leonardoward/gps-development-boards/Images/IMG_20210819_091816.jpg

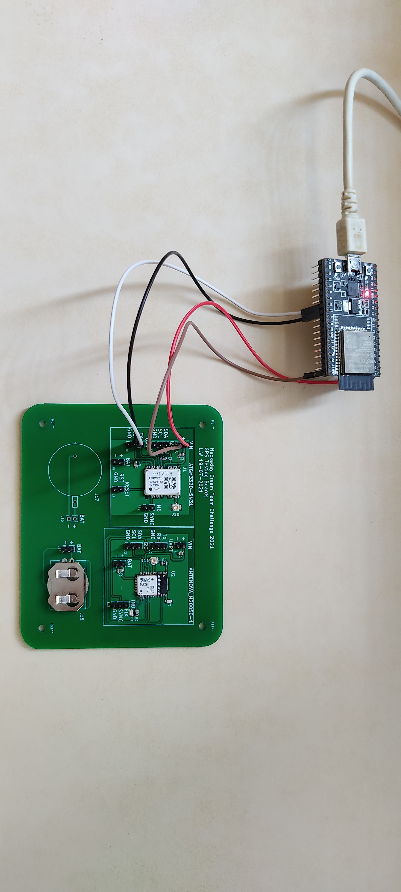
Images/IMG_20210819_091816.jpg
