leonardoward/gps-development-boards/Images/IMG_20210819_091819.jpg

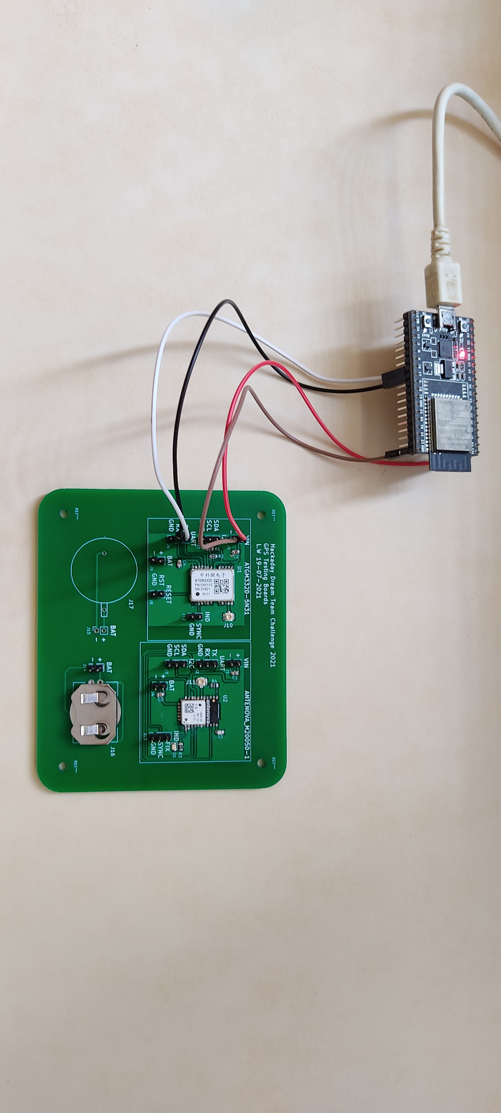
Images/IMG_20210819_091819.jpg
