leonardoward/gps-development-boards/Images/IMG_20210819_091824.jpg

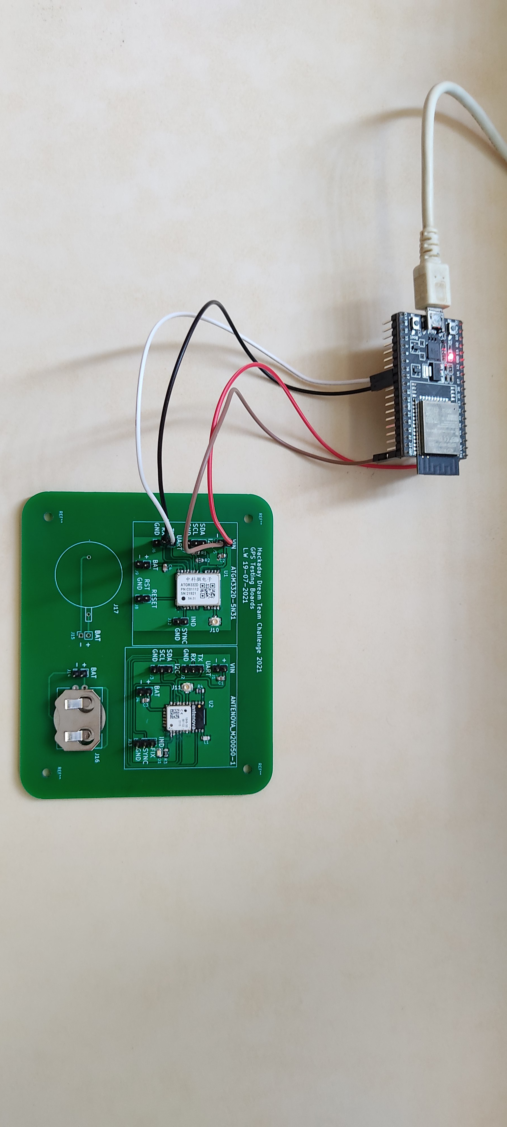
Images/IMG_20210819_091824.jpg
