leonardoward/gps-development-boards/Images/IMG_20210819_091829.jpg

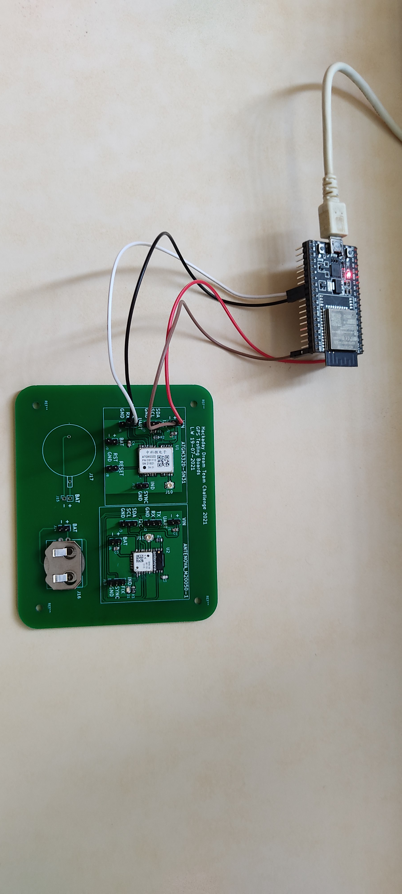
Images/IMG_20210819_091829.jpg
