leonardoward/gps-development-boards/Images/IMG_20210819_091835.jpg

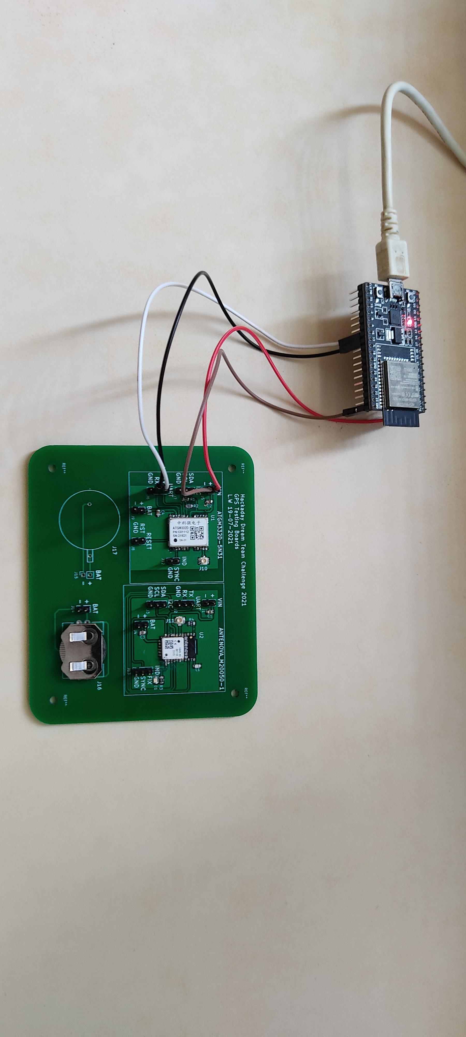
Images/IMG_20210819_091835.jpg
