leonardoward/gps-development-boards/Images/IMG_20210819_091837.jpg

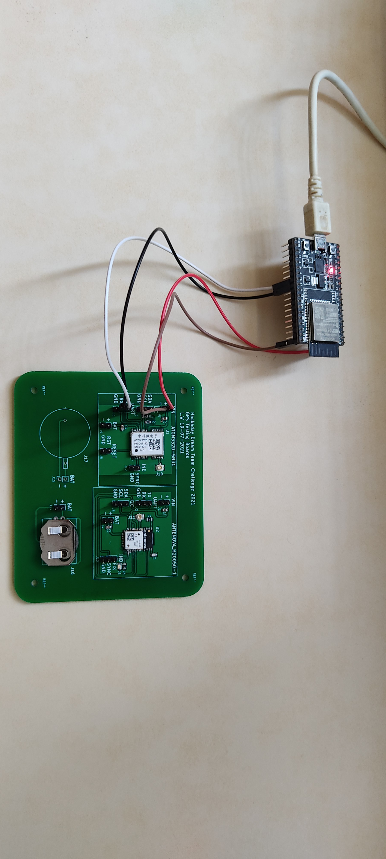
Images/IMG_20210819_091837.jpg
