leonardoward/gps-development-boards/Images/IMG_20210819_092154.jpg

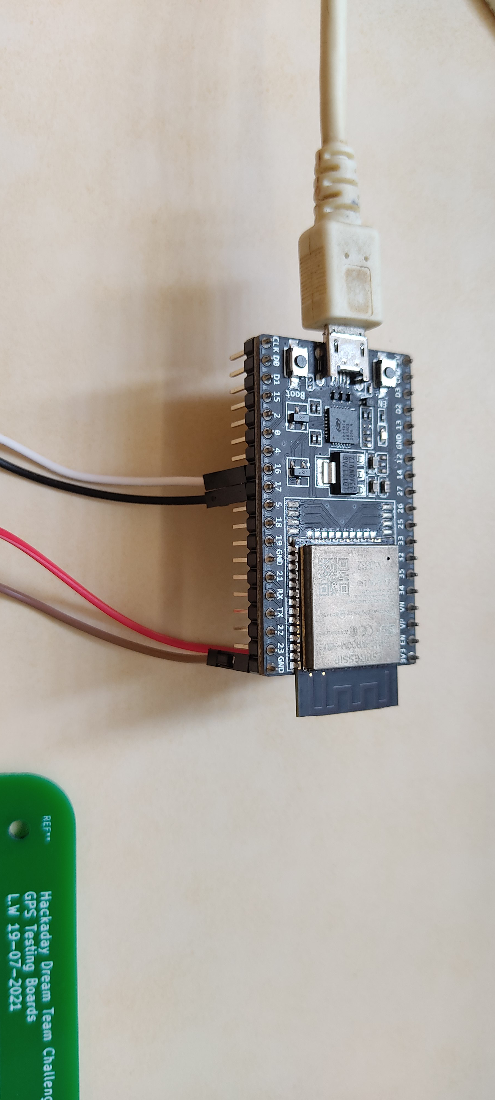
Images/IMG_20210819_092154.jpg
