leonardoward/gps-development-boards/Images/IMG_20210819_092156.jpg

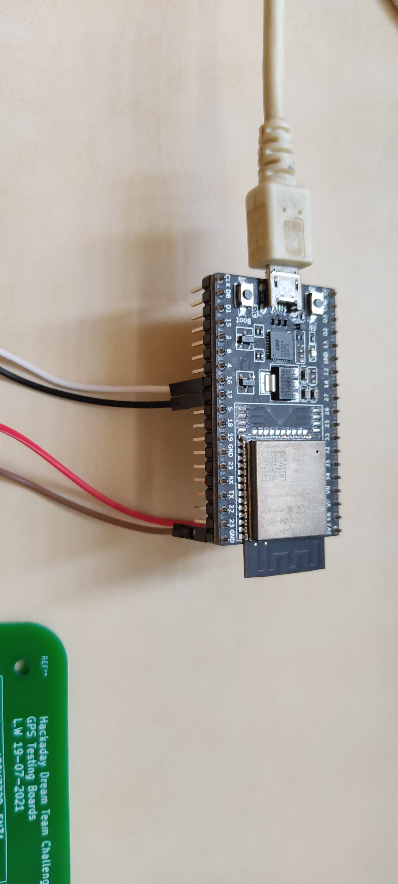
Images/IMG_20210819_092156.jpg
