leonardoward/gps-development-boards/Images/IMG_20210819_092208.jpg

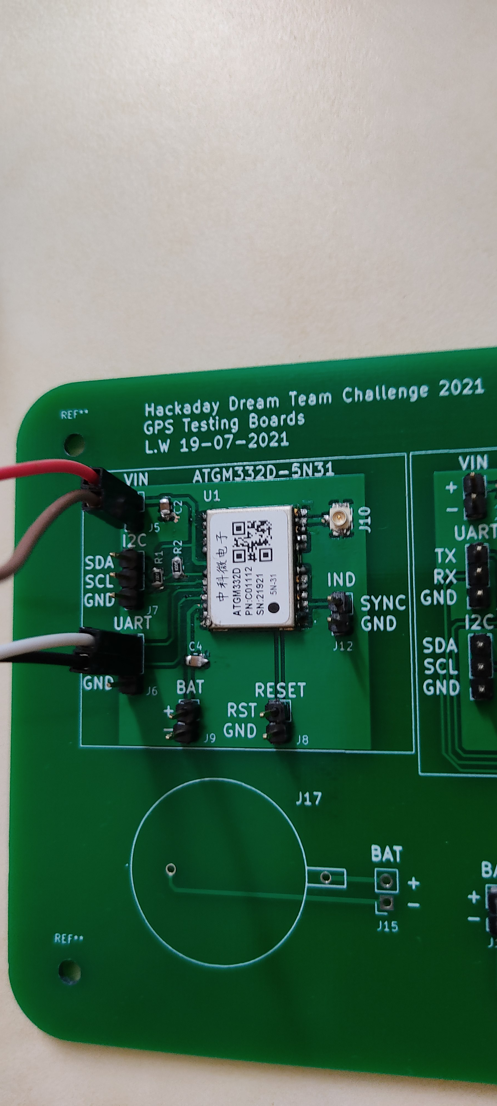
Images/IMG_20210819_092208.jpg
