leonardoward/gps-development-boards/Images/IMG_20210819_092211.jpg

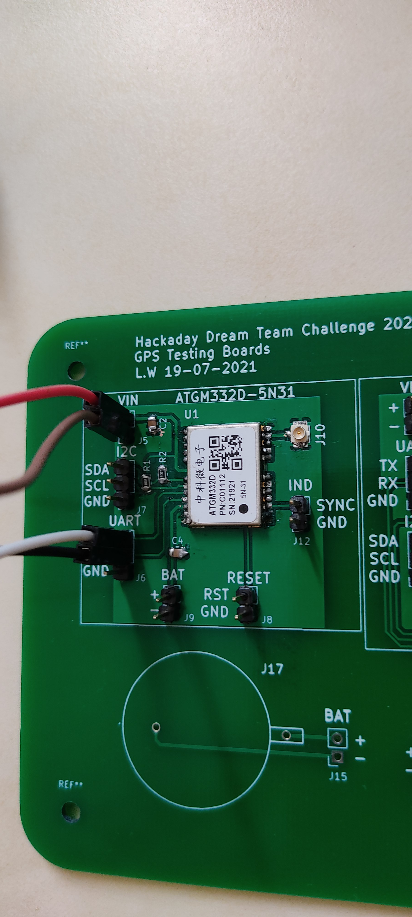
Images/IMG_20210819_092211.jpg
